lucasliano/Gimbal/EntregaFinal/FotosGimbal/download.jpg

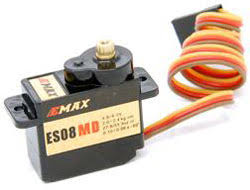
EntregaFinal/FotosGimbal/download.jpg
