lucasliano/Gimbal/EntregaFinal/FotosGimbal/Gimbal atras.png

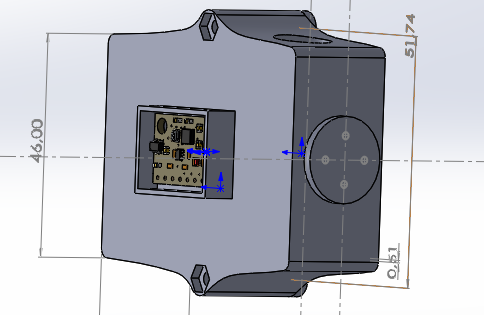
EntregaFinal/FotosGimbal/Gimbal atras.png
