lucasliano/Gimbal/EntregaFinal/FotosGimbal/micro-servo-tower-pro-sg90-12kg-robotica-arduino-raspberry-D_NQ_NP_827429-MLA31112139410_062019-F.webp

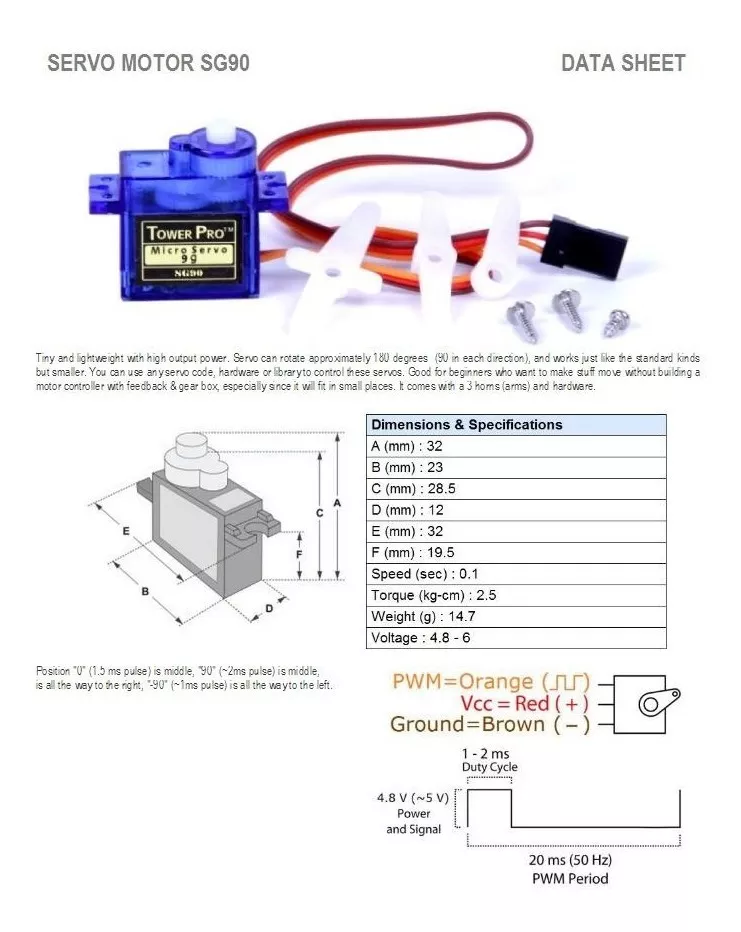
EntregaFinal/FotosGimbal/micro-servo-tower-pro-sg90-12kg-robotica-arduino-raspberry-D_NQ_NP_827429-MLA31112139410_062019-F.webp
