lucasliano/Gimbal/EntregaFinal/FotosGimbal/mini-servo-sg90-9g-robotica-arduino-servomotor-x10-unidades-D_NQ_NP_653291-MLA31336453937_072019-F.jpg

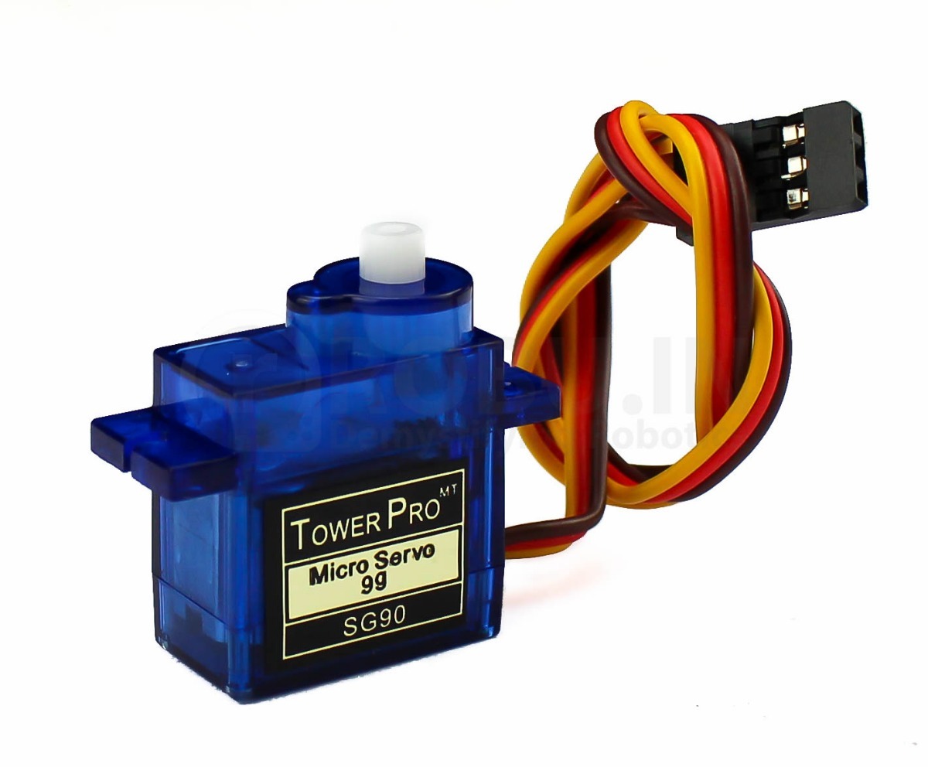
EntregaFinal/FotosGimbal/mini-servo-sg90-9g-robotica-arduino-servomotor-x10-unidades-D_NQ_NP_653291-MLA31336453937_072019-F.jpg
