lucasliano/Gimbal/EntregaFinal/FotosGimbal/PID_es_updated_feedback.svg.png

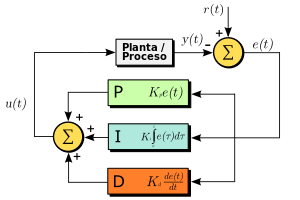
EntregaFinal/FotosGimbal/PID_es_updated_feedback.svg.png
