lucasliano/Gimbal/Fotos/Gimbal2.JPG

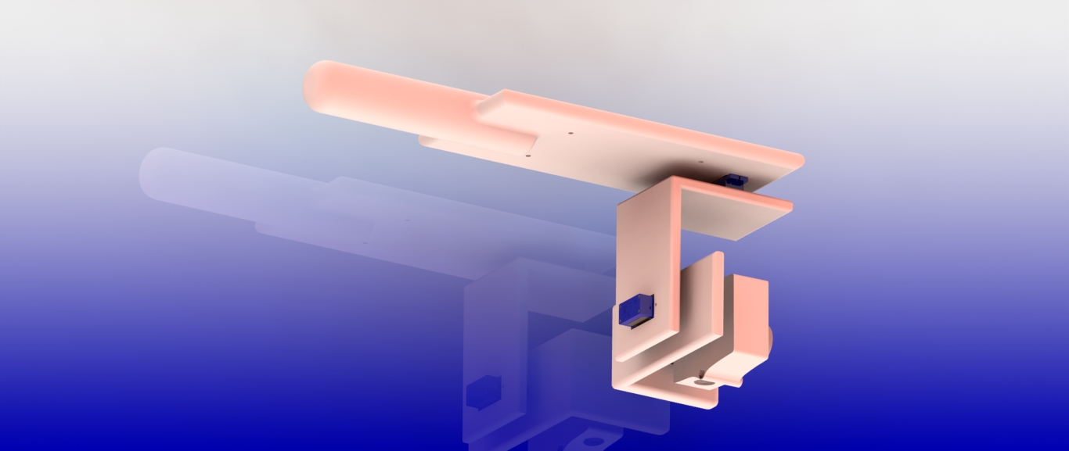
Fotos/Gimbal2.JPG
