lucasliano/Gimbal/Fotos/GUI-Desactivado.png

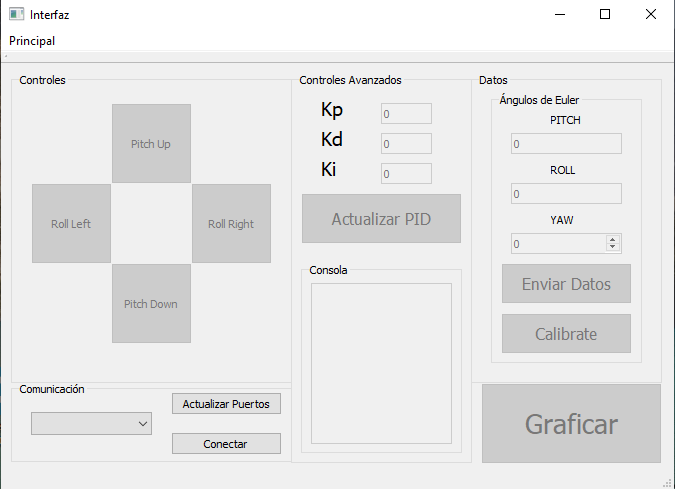
Fotos/GUI-Desactivado.png
