lucasliano/Gimbal/Fotos/GUI-Graficos.png

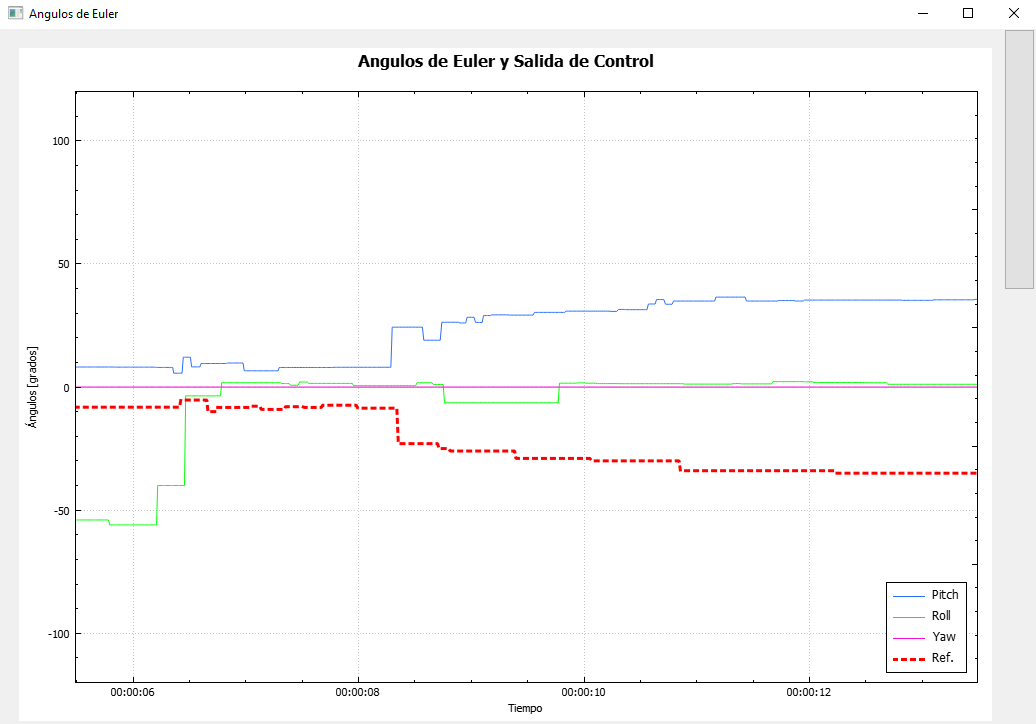
Fotos/GUI-Graficos.png
