lucasliano/Gimbal/Piezas 3D/v3.0/Piezas externas/Servos/SG90/SG90 - Micro Servo 9g - Tower Pro.5.SLDPRT

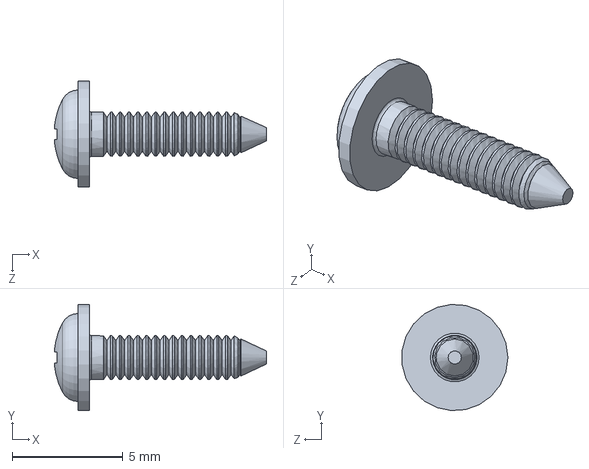
[picture p58: CAD file, 2019-12-19]
Piezas 3D/v3.0/Piezas externas/Servos/SG90/SG90 - Micro Servo 9g - Tower Pro.5.SLDPRT
9.57 x 4.79 x 4.78 mm
