lucasliano/Gimbal/Piezas 3D/v3.0/Piezas externas/Servos/SG90/SG90 - Micro Servo 9g - Tower Pro.2.SLDPRT

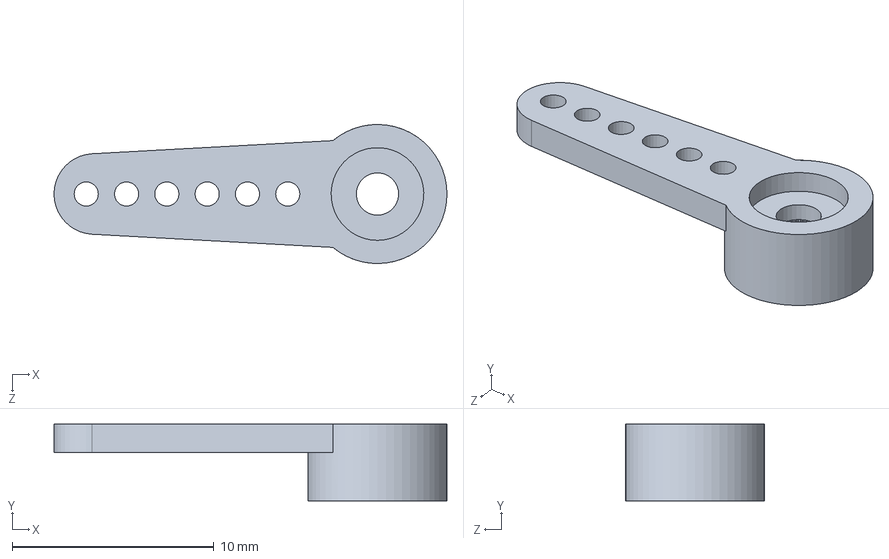
[picture p59: CAD file, 2019-12-19]
Piezas 3D/v3.0/Piezas externas/Servos/SG90/SG90 - Micro Servo 9g - Tower Pro.2.SLDPRT
19.5 x 3.80 x 6.90 mm
