lucasliano/Gimbal/GUI/ProyectoQt/build-Interfaz-Desktop_Qt_5_12_2_MSVC2017_32bit-Debug/Screenshots/Screenshot.png

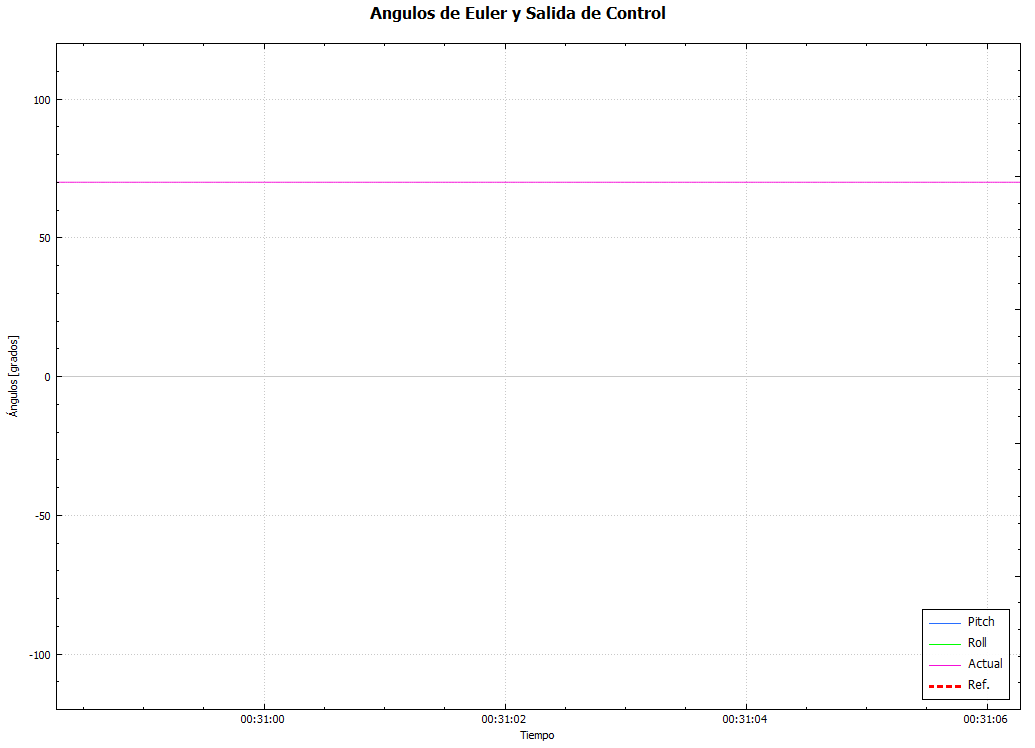
GUI/ProyectoQt/build-Interfaz-Desktop_Qt_5_12_2_MSVC2017_32bit-Debug/Screenshots/Screenshot.png
