lucasliano/Gimbal/Codigo/inc/Drivers/DR_gpio.h

/*******************************************************************************************************************************//**
 *
 * @file		Infotronic.h
 * @brief		Macros, tipos , prototipos, de la aplicacion
 * @date		23-03-16
 * @author		Marcelo Trujillo
 *
 **********************************************************************************************************************************/

/***********************************************************************************************************************************
 *** MODULO
 **********************************************************************************************************************************/

#ifndef DR_GPIO_H_
#define DR_GPIO_H_

#ifdef __cplusplus
extern "C" {
#endif


#include "all.h"

/***********************************************************************************************************************************
 *** INCLUDES GLOBALES
 **********************************************************************************************************************************/

/***********************************************************************************************************************************
 *** DEFINES GLOBALES
 **********************************************************************************************************************************/

/***********************************************************************************************************************************
 *** MACROS GLOBALES
 **********************************************************************************************************************************/

#define 	ALTO	1
#define 	BAJO	0
#define 	SALIDA	1
#define 	ENTRADA	0

#define 	FUNCION_GPIO		0
#define 	FUNCION_1			1
#define 	FUNCION_2			2
#define 	FUNCION_3			3

#define 	PULLUP				0
#define 	REPEATER			1
#define 	NONE				2
#define 	PULLDOWN			3

/***********************************************************************************************************************************
 *** TIPO DE DATOS GLOBALES
 **********************************************************************************************************************************/

/***********************************************************************************************************************************
 *** VARIABLES GLOBALES
 **********************************************************************************************************************************/

/***********************************************************************************************************************************
 *** PROTOTIPOS DE FUNCIONES GLOBALES
 **********************************************************************************************************************************/
void SetDIR ( uint8_t puerto , uint8_t bit , uint8_t dir );
void SetMODE ( uint8_t puerto , uint8_t bit , uint8_t modo );
void SetPIN ( uint8_t puerto , uint8_t bit , uint8_t estado );
uint8_t GetPIN( uint8_t puerto , uint8_t bit , uint8_t actividad );


#ifdef __cplusplus
}
#endif

#endif /* DR_GPIO_H_ */
