lucasliano/Gimbal/Codigo/inc/Drivers/DR_lcd.h

/*******************************************************************************************************************************//**
 *
 * @file		FW_lcd.h
 * @brief		DESCRIPCION ------------------------
 * @date		8/11/2016
 * @author		Ing. Marcelo Trujillo
 *
 **********************************************************************************************************************************/

/***********************************************************************************************************************************
 *** MODULO
 **********************************************************************************************************************************/
#ifndef SOURCES_FIRMWARE_TK_FW_LCD_H_
#define SOURCES_FIRMWARE_TK_FW_LCD_H_

#ifdef __cplusplus
extern "C" {
#endif


/***********************************************************************************************************************************
 *** INCLUDES GLOBALES
 **********************************************************************************************************************************/
#include "all.h"

/***********************************************************************************************************************************
 *** DEFINES GLOBALES
 **********************************************************************************************************************************/
#define		LCD_CONTROL		1
#define		LCD_DATA		0

#define 	LCD_BUFFER_SIZE	340

#define	 	LCD_LINE_SIZE	20
#define 	LCD_LINES		2

#define 	DSP0			0
#define 	DSP1			1

#define 	LINE_1_ADDRESS	0x00
#define 	LINE_2_ADDRESS	0x40
/***********************************************************************************************************************************
 *** MACROS GLOBALES
 **********************************************************************************************************************************/

/***********************************************************************************************************************************
 *** TIPO DE DATOS GLOBALES
 **********************************************************************************************************************************/

/***********************************************************************************************************************************
 *** VARIABLES GLOBALES
 **********************************************************************************************************************************/
extern uint32_t volatile lcdDelay;

/***********************************************************************************************************************************
 *** PROTOTIPOS DE FUNCIONES GLOBALES
 **********************************************************************************************************************************/
void InicializarLCD( void );
int8_t LCD_Push( uint8_t data , uint8_t control );
int16_t LCD_Pop( void );
void EscrituraLCD( void );


#ifdef __cplusplus
}
#endif
#endif /* SOURCES_FIRMWARE_TK_FW_LCD_H_ */
