lucasliano/Gimbal/Codigo/src/Drivers/DR_gpio.c

/*******************************************************************************************************************************//**
 *
 * @file		Infotronic.c
 * @brief		Drivers de GPIO LPC1769
 * @date		23-03-16
 * @author		Marcelo Trujillo
 *
 **********************************************************************************************************************************/

/***********************************************************************************************************************************
 *** INCLUDES
 **********************************************************************************************************************************/
#include "all.h"

/***********************************************************************************************************************************
 *** DEFINES PRIVADOS AL MODULO
 **********************************************************************************************************************************/

/***********************************************************************************************************************************
 *** MACROS PRIVADAS AL MODULO
 **********************************************************************************************************************************/

/***********************************************************************************************************************************
 *** TIPOS DE DATOS PRIVADOS AL MODULO
 **********************************************************************************************************************************/

/***********************************************************************************************************************************
 *** TABLAS PRIVADAS AL MODULO
 **********************************************************************************************************************************/

/***********************************************************************************************************************************
 *** VARIABLES GLOBALES PUBLICAS
 **********************************************************************************************************************************/

/***********************************************************************************************************************************
 *** VARIABLES GLOBALES PRIVADAS AL MODULO
 **********************************************************************************************************************************/

/***********************************************************************************************************************************
 *** PROTOTIPO DE FUNCIONES PRIVADAS AL MODULO
 **********************************************************************************************************************************/

 /***********************************************************************************************************************************
 *** FUNCIONES PRIVADAS AL MODULO
 **********************************************************************************************************************************/

 /***********************************************************************************************************************************
 *** FUNCIONES GLOBALES AL MODULO
 **********************************************************************************************************************************/
/**
	\fn  void SetDIR ( uint8_t puerto , uint8_t bit , uint8_t dir )
	\brief Selecciona si el GPIO sera entrada o salida
 	\date 30/06/2019
 	\param [in] puerto Numero del puerto seleccionado
 	\param [in] bit Numero del bit seleccionado
 	\param [in] dir seleccion entre entrada o salida

	\return void
*/
void SetDIR ( uint8_t puerto , uint8_t bit , uint8_t dir )
{
	__RW uint32_t *p = ( __RW uint32_t * )  0x2009C000 ;

	if ( dir )
		*( p + puerto * 8 ) = *( p + puerto * 8 ) | ( 1 << bit );
	else
		*( p + puerto * 8 ) = *( p + puerto * 8 ) & ( ~ ( 1 << bit ) );

}

/**
	\fn  void SetPIN ( uint8_t puerto , uint8_t bit , uint8_t estado )
	\brief Activa/Desactiva un pin
 	\date 30/06/2019
 	\param [in] puerto Numero del puerto seleccionado
 	\param [in] bit Numero del bit seleccionado
 	\param [in] estado 1: ON 2:OFF

	\return void
*/
void SetPIN ( uint8_t puerto , uint8_t bit , uint8_t estado )
{
	__RW uint32_t *set = ( __RW uint32_t * )  0x2009C018 ;
	__RW uint32_t *clear = ( __RW uint32_t * )  0x2009C01C ;

	if (estado)
		*( set + puerto * 8 ) = *( set + puerto * 8 ) | ( 1 << bit );
	else
		*( clear + puerto * 8 ) = *( clear + puerto * 8 ) | ( 1 << bit );

}


uint8_t GetPIN( uint8_t puerto , uint8_t bit , uint8_t actividad )
{
	__RW uint32_t *p = ( __RW uint32_t * )  0x2009C014 ;
	uint8_t r;

	r = ( *( p + puerto * 8 ) >> bit ) & 1;
	if ( actividad )
		return r;
	return !r;
}
