lucasliano/Gimbal/Codigo/inc/Drivers/I2C.h

/**
  \file i2c.h
  \brief Declaración de rutinas, defines y direcciones de memoria asociados al manejo de registros i2c.
  \author Grupo 8 - R2003
  \date 2019.10.19
  \version 1.2
*/

#ifndef I2C_H_
#define I2C_H_

#ifdef __cplusplus
extern "C" {
#endif

#include "all.h"







#ifdef __cplusplus
}
#endif

#endif /* I2C_H_ */
