lucasliano/Gimbal/GUI/ProyectoQt/Interfaz/main.cpp

#include <QApplication>
#include <QSplashScreen>
#include <QTimer>
#include "interfaz.h"

double pitch = 0;
double roll = 0;
double yaw = 0;
double out = 0;
int index=0;
QByteArray bufferCircular;
int main(int argc, char *argv[])
{
    QApplication a(argc, argv);
    bufferCircular.clear();


    //Esto de acá inicializa la imagen que va a saltar
    QSplashScreen *splash = new QSplashScreen;
    splash->setPixmap(QPixmap("img/inicio.jpeg"));
    splash->show(); //Se muestra la imagen

    Interfaz w; //Inicializo la ventana "interfaz"

    //Lanzo dos timers para que se muestre la imagen de inicio y dsps inicie la ventana.

    QTimer::singleShot(2500,splash,SLOT(close()));//Muestro la foto del gimbal
    QTimer::singleShot(2500,&w,SLOT(show()));




    return a.exec();
}
